kicker22004/Dexcom-G6-Mag-Recharge/Images/IMG_20200726_133625.jpg

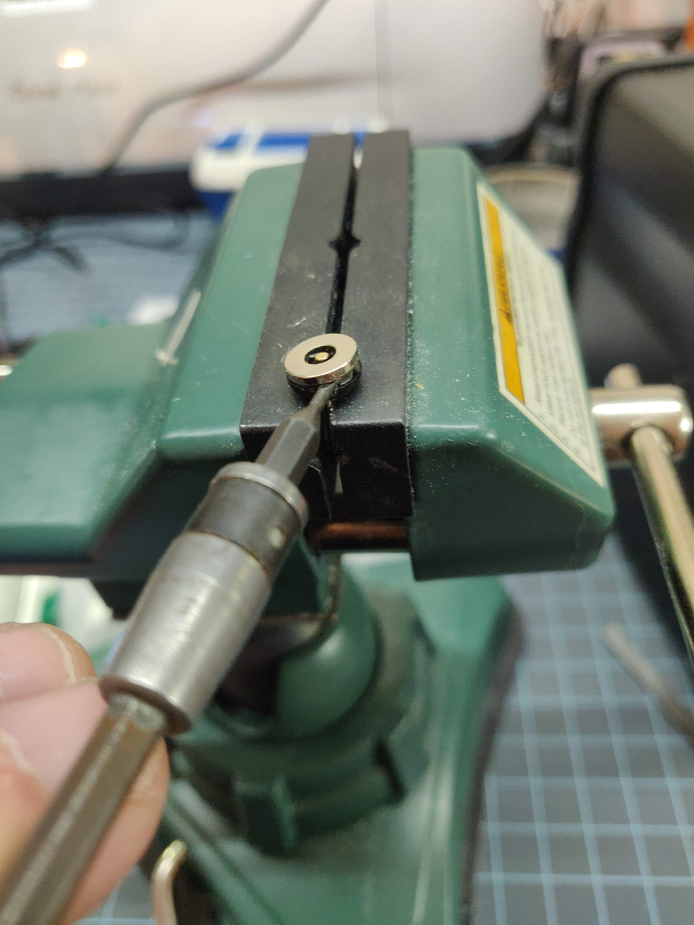
Images/IMG_20200726_133625.jpg
