kicker22004/Dexcom-G6-Mag-Recharge/Images/IMG_20200802_224226.jpg

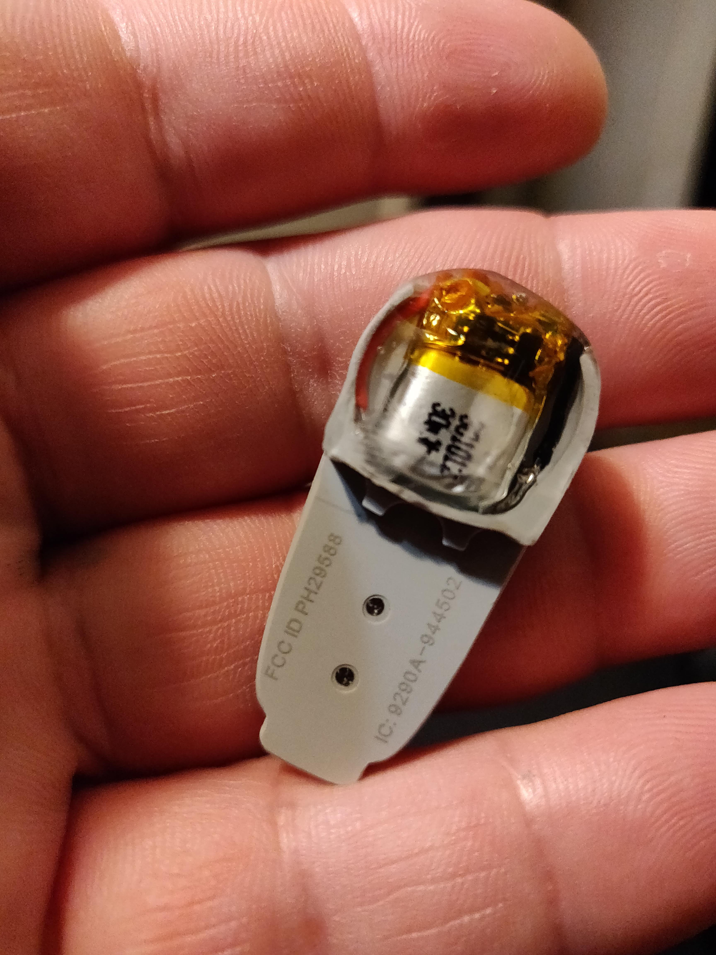
Images/IMG_20200802_224226.jpg
