kicker22004/Dexcom-G6-Mag-Recharge/Images/IMG_20200726_135140.jpg

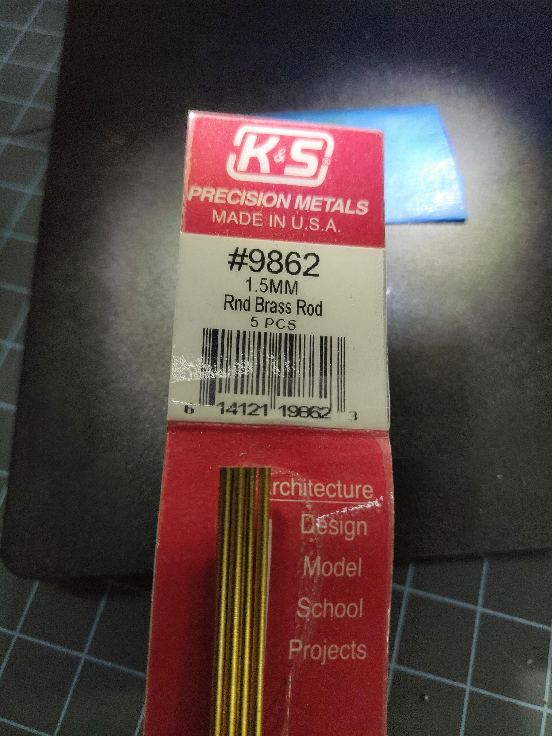
Images/IMG_20200726_135140.jpg
