kicker22004/Dexcom-G6-Mag-Recharge/Images/IMG_20200802_152115.jpg

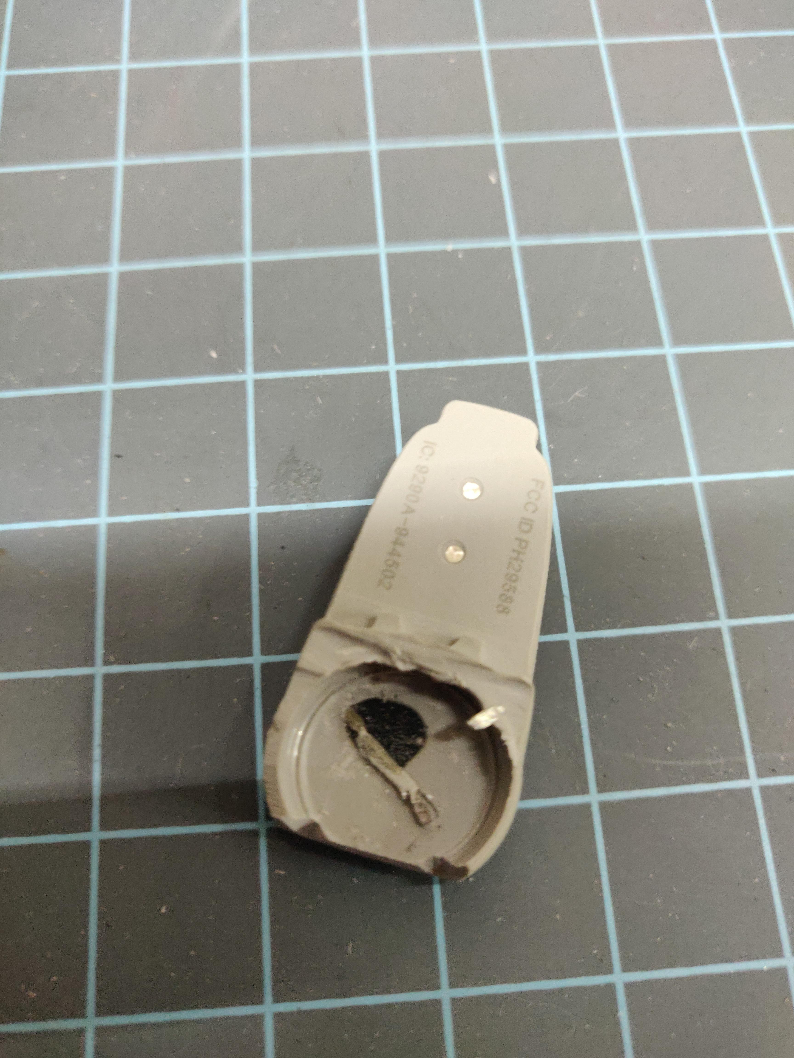
Images/IMG_20200802_152115.jpg
