kicker22004/Dexcom-G6-Mag-Recharge/Images/IMG_20200802_172058.jpg

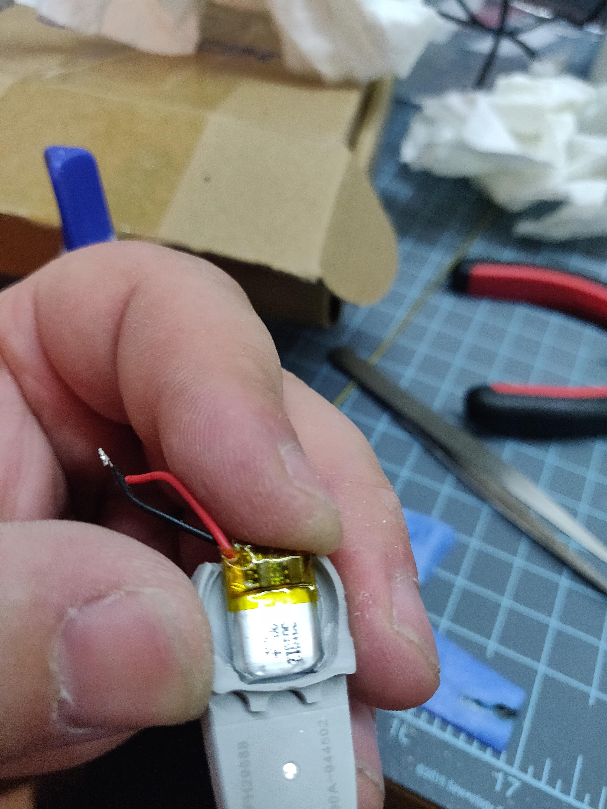
Images/IMG_20200802_172058.jpg
