kicker22004/Dexcom-G6-Mag-Recharge/Images/IMG_20200802_224211.jpg

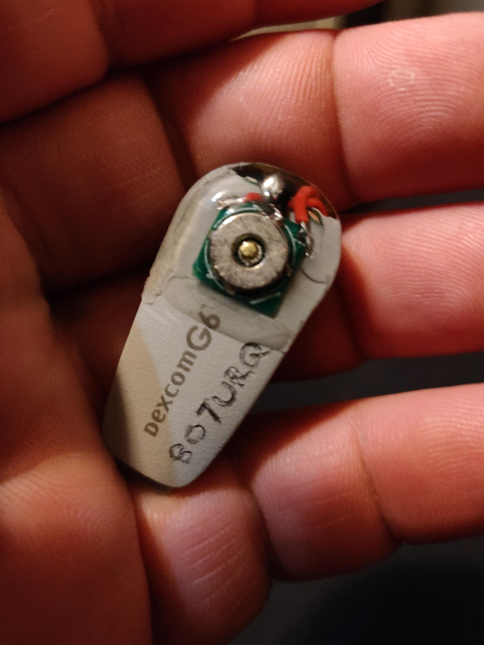
Images/IMG_20200802_224211.jpg
